EBSPhysik2020/Photometer/LED/LED Schaltung.png

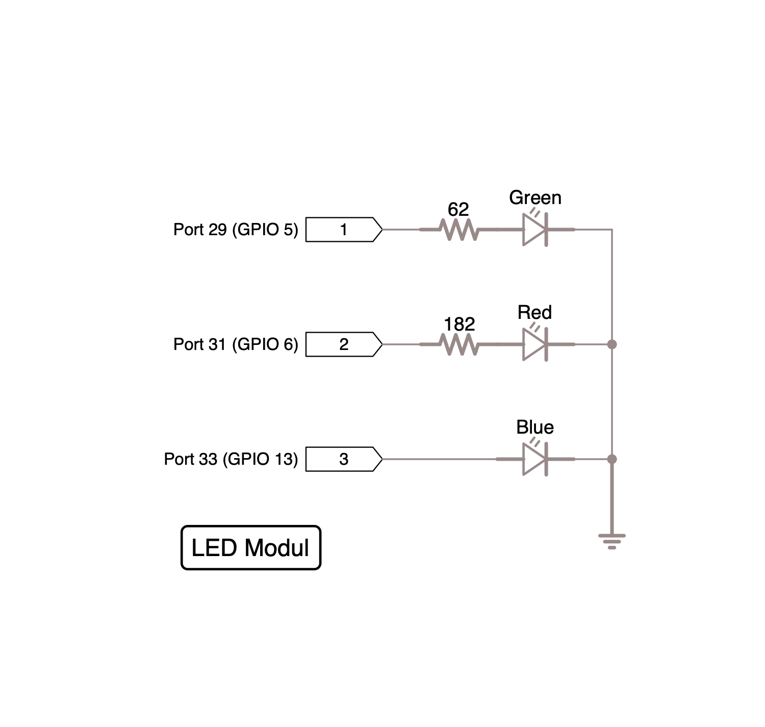
LED/LED Schaltung.png
