EBSPhysik2020/Photometer/Software/assets/0.png

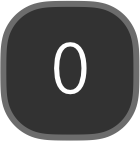
Software/assets/0.png
