EBSPhysik2020/Photometer/Software/assets/1.png

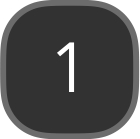
Software/assets/1.png
