EBSPhysik2020/Photometer/Software/assets/7.png

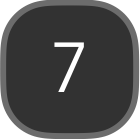
Software/assets/7.png
