EBSPhysik2020/Photometer/Software/assets/comma.png

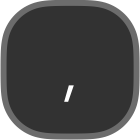
Software/assets/comma.png
