EBSPhysik2020/Photometer/Software/assets/radio.png

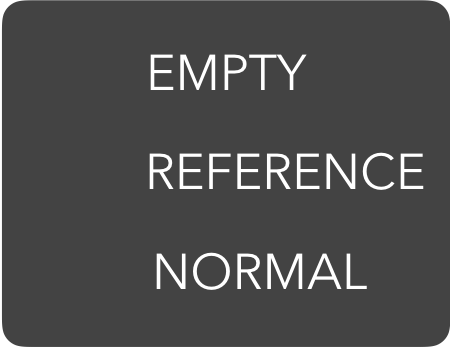
Software/assets/radio.png
