EBSPhysik2020/Photometer/Software/assets/ref_label.png

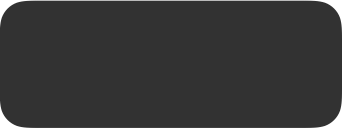
Software/assets/ref_label.png
