EBSPhysik2020/Photometer/Software/assets/start.png

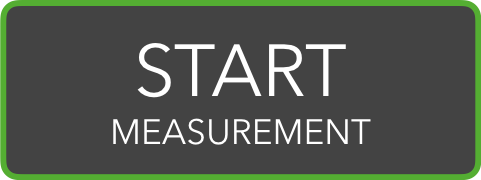
Software/assets/start.png
